e-sp9/kobu/case/thumb-bottom-plate.stl

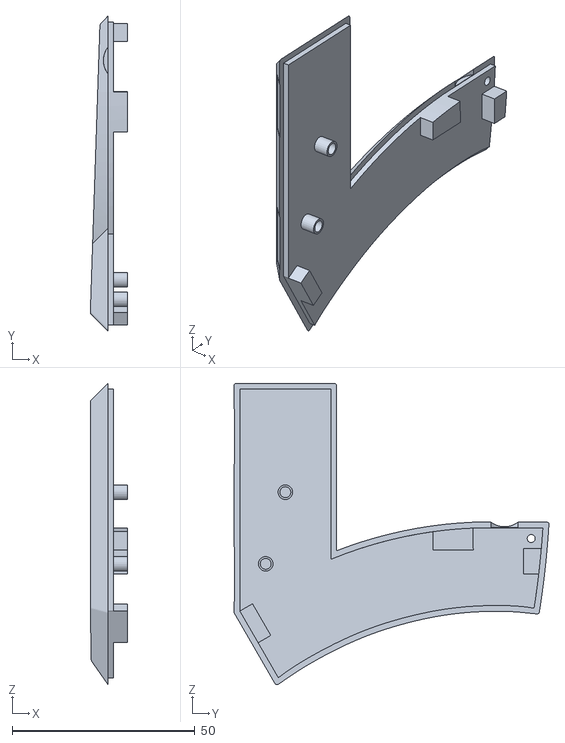
[picture p15: CAD file, 2026-05-19]
case/thumb-bottom-plate.stl
10.2 x 86.2 x 82.4
