e-sp9/kobu/case/stl/common/power-switch.stl

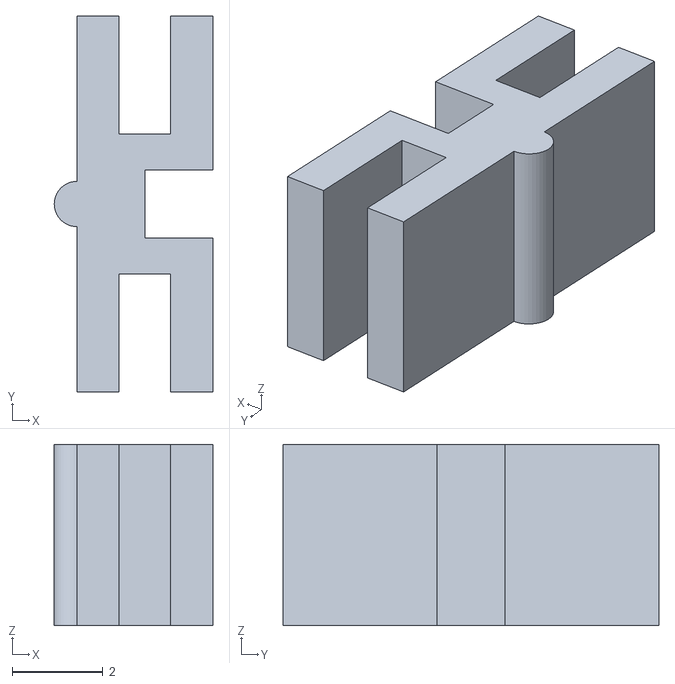
[picture p16: CAD file, 2026-06-01]
case/stl/common/power-switch.stl
3.50 x 8.30 x 4.00
