e-sp9/kobu/case/stl/thumb/thumb-bottom-plate.stl

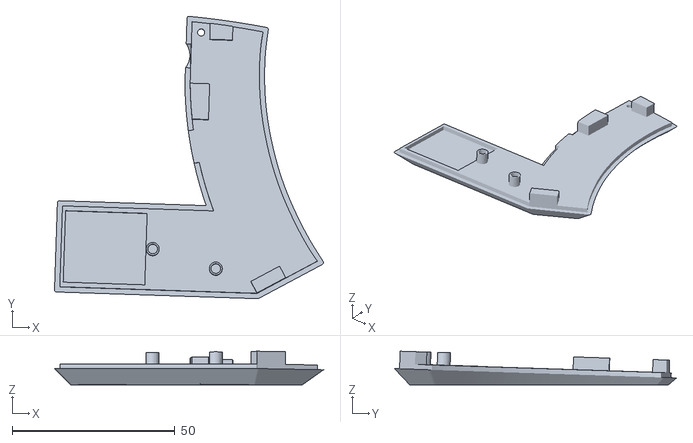
[picture p17: CAD file, 2026-06-01]
case/stl/thumb/thumb-bottom-plate.stl
82.8 x 86.9 x 10.3
