e-sp9/kobu/case/stl/thumb/thumb-side-plate.stl

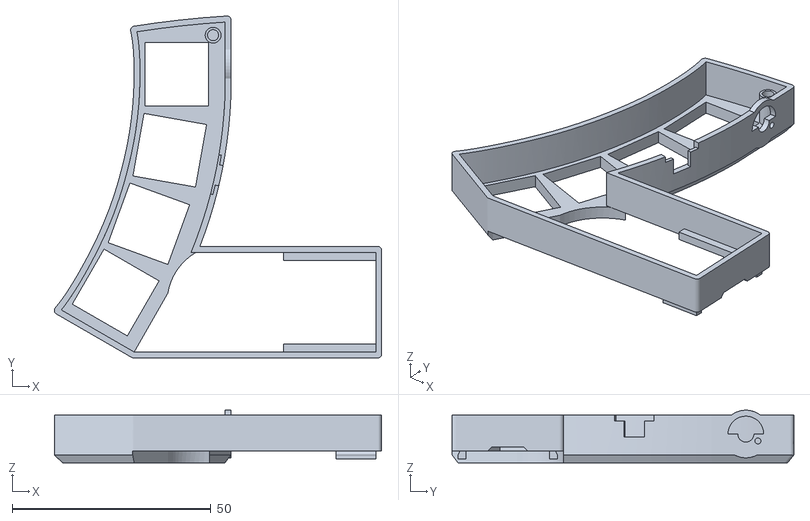
[picture p18: CAD file, 2026-06-01]
case/stl/thumb/thumb-side-plate.stl
82.5 x 86.1 x 13.2
