e-sp9/kobu/case/stl/thumb/track-ball-case.stl

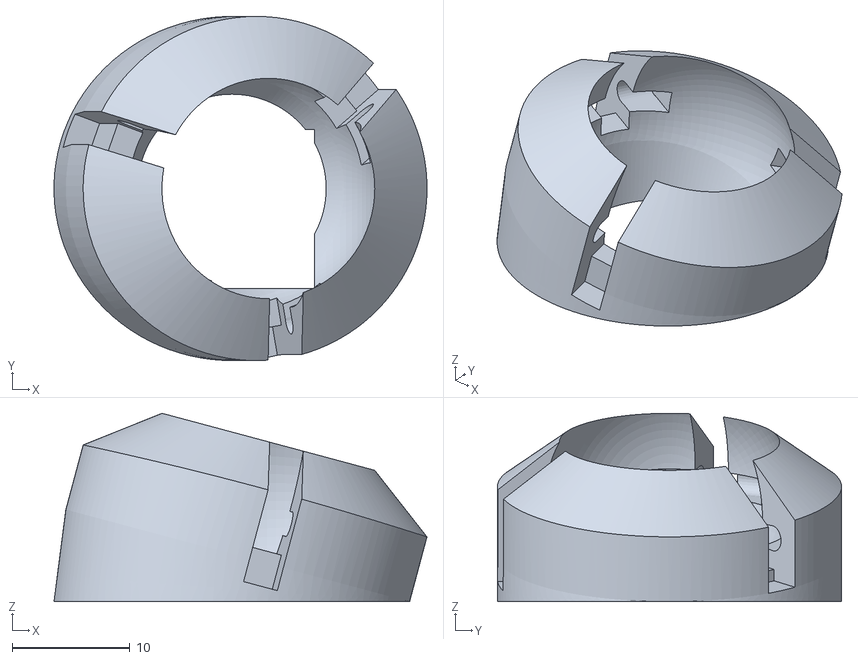
[picture p19: CAD file, 2026-06-01]
case/stl/thumb/track-ball-case.stl
31.6 x 29.2 x 16.0
