e-sp9/kobu/case/thumb-side-plate.stl

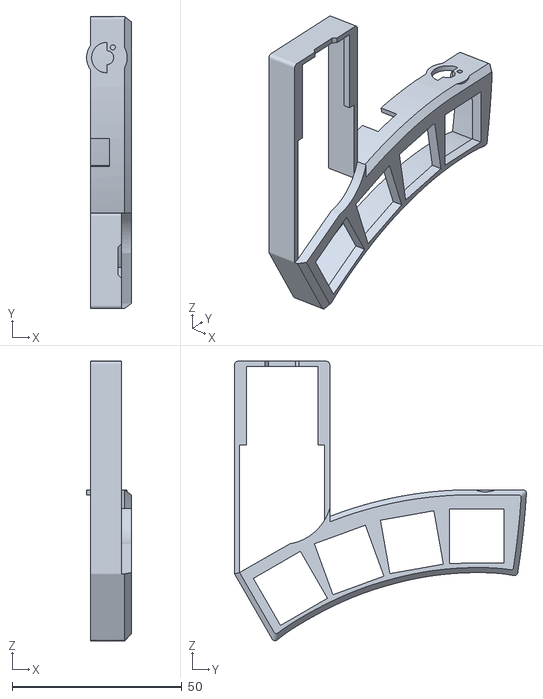
[picture p20: CAD file, 2026-05-19]
case/thumb-side-plate.stl
13.2 x 86.1 x 82.5
